Global-Health-Engineering/sitting-UDDT/drawings/user_interface_over_seat.pdf

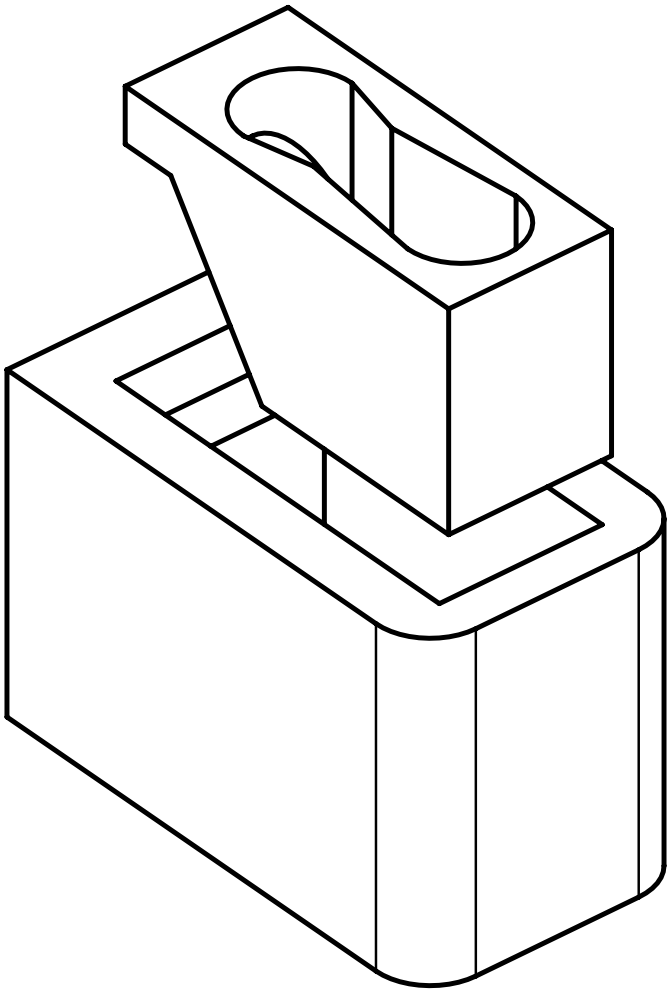
[picture p9: figure]
