Global-Health-Engineering/sitting-UDDT/drawings/EOOS_child_tech_4.pdf

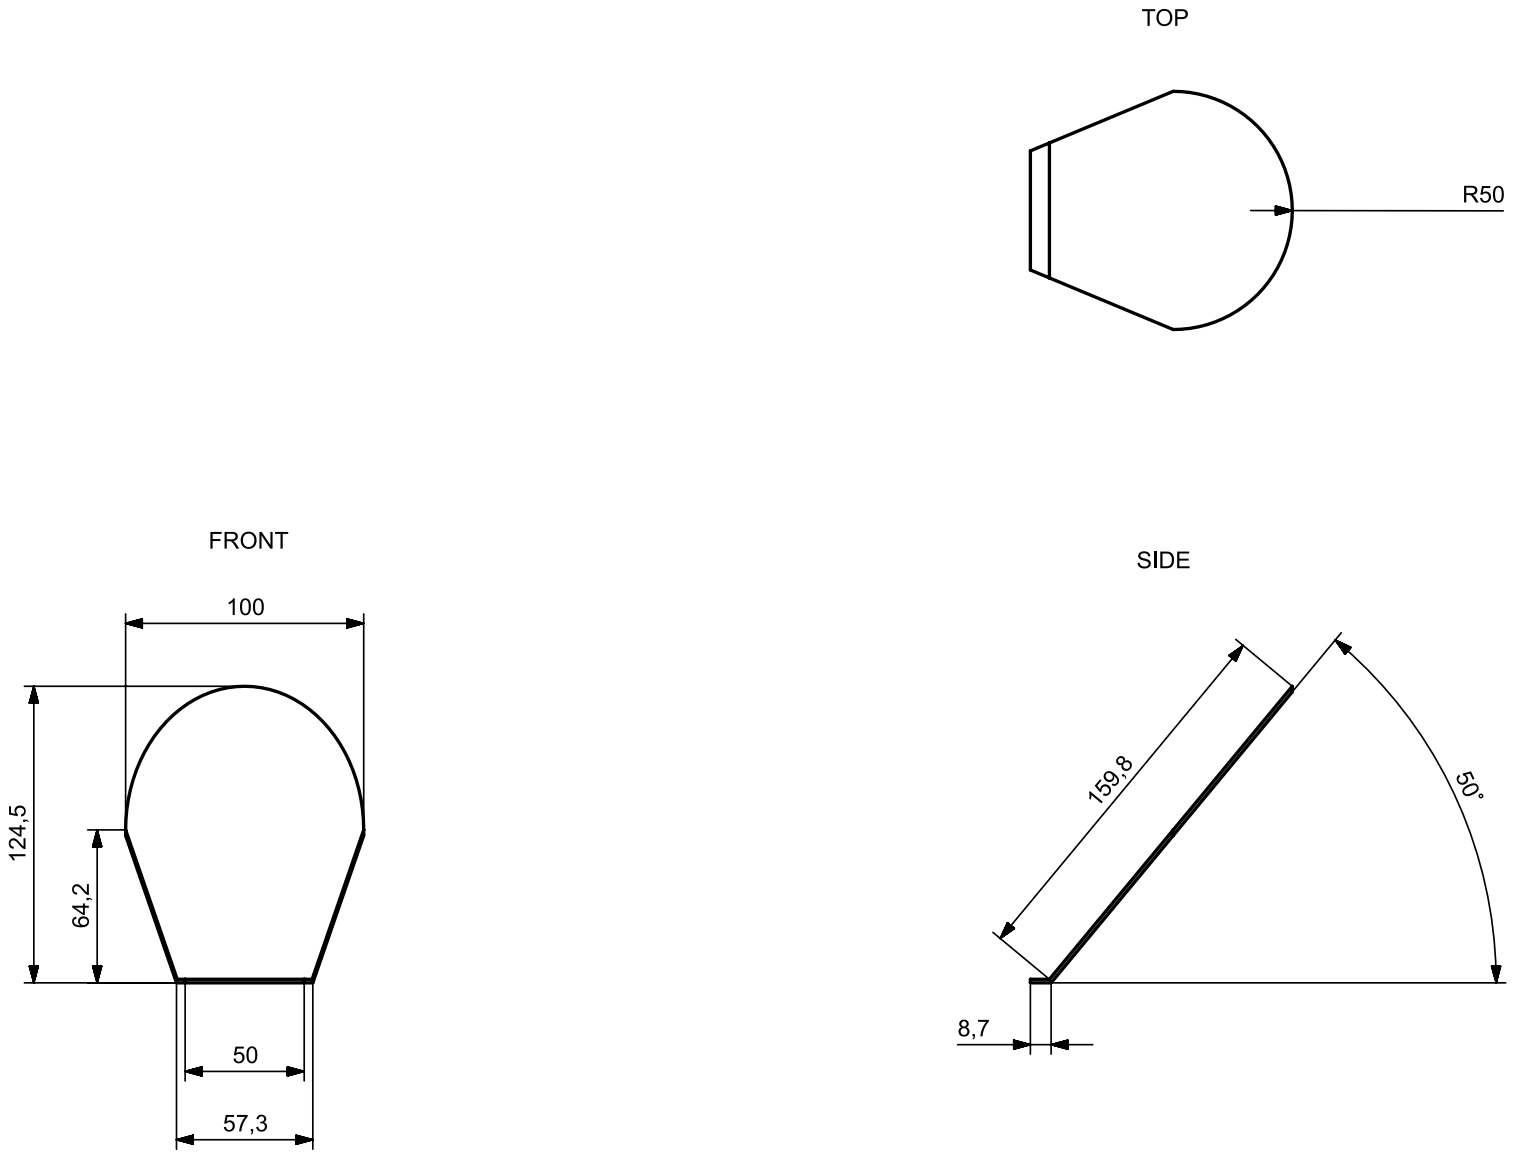
[picture p26: page 1]
