Global-Health-Engineering/sitting-UDDT/drawings/EOOS_child_tech_5.pdf

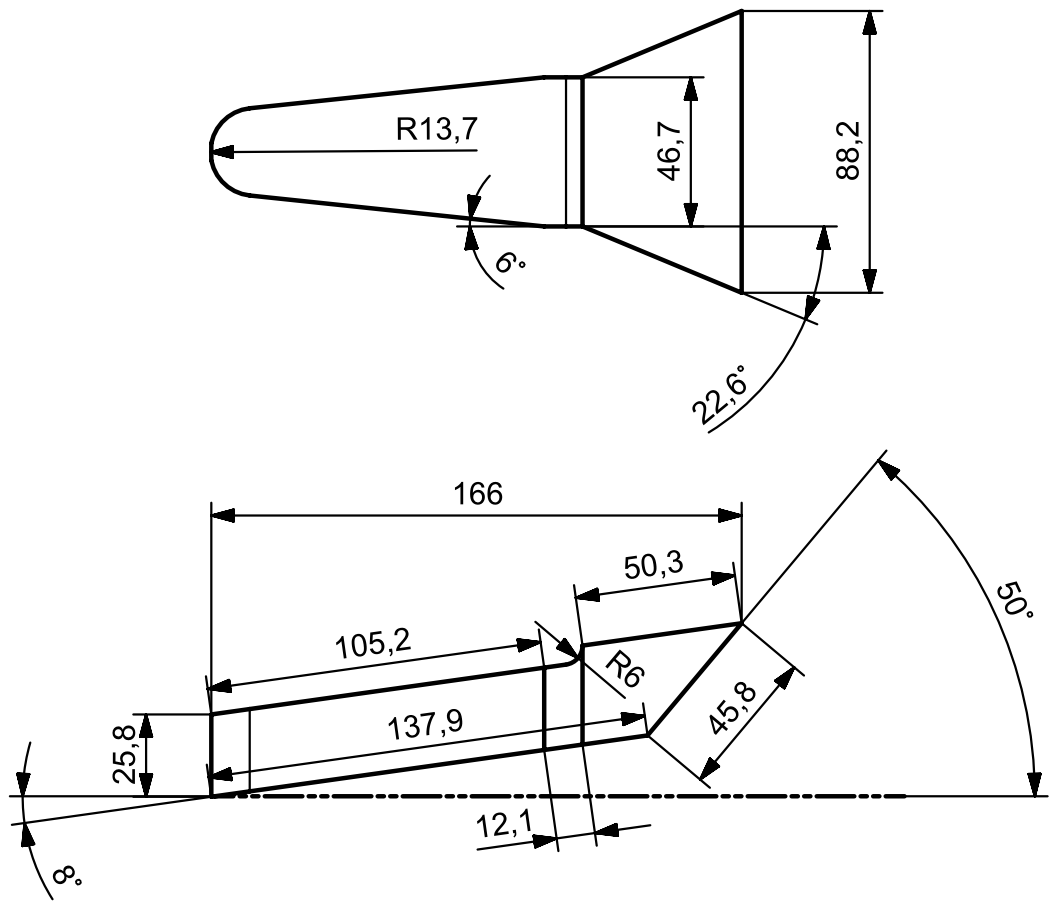
[picture p27: page 1]
