Global-Health-Engineering/sitting-UDDT/drawings/EOOS_child_tech_6.pdf

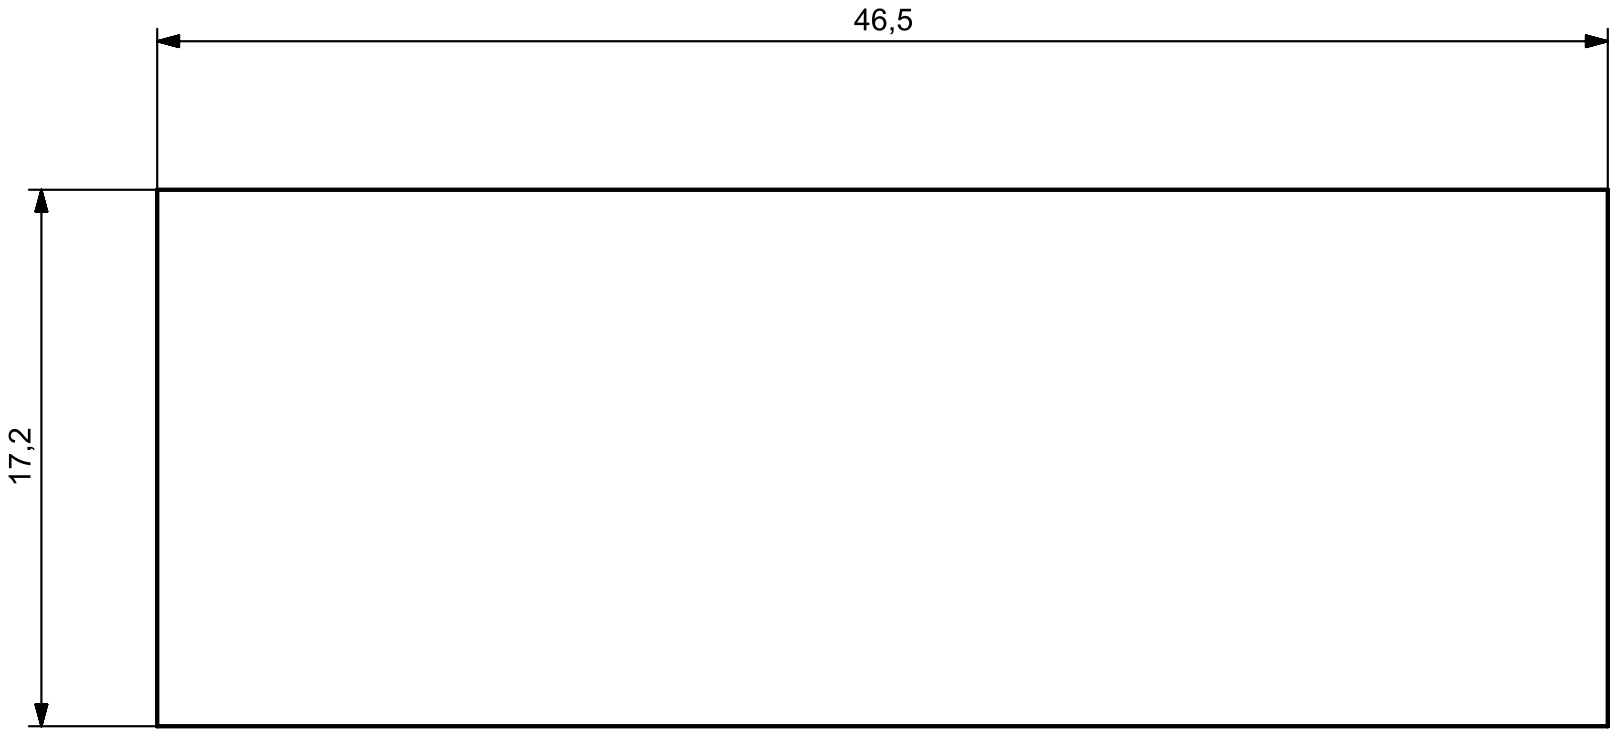
[picture p28: page 1]
