Global-Health-Engineering/sitting-UDDT/drawings/tech_seat_adult.pdf

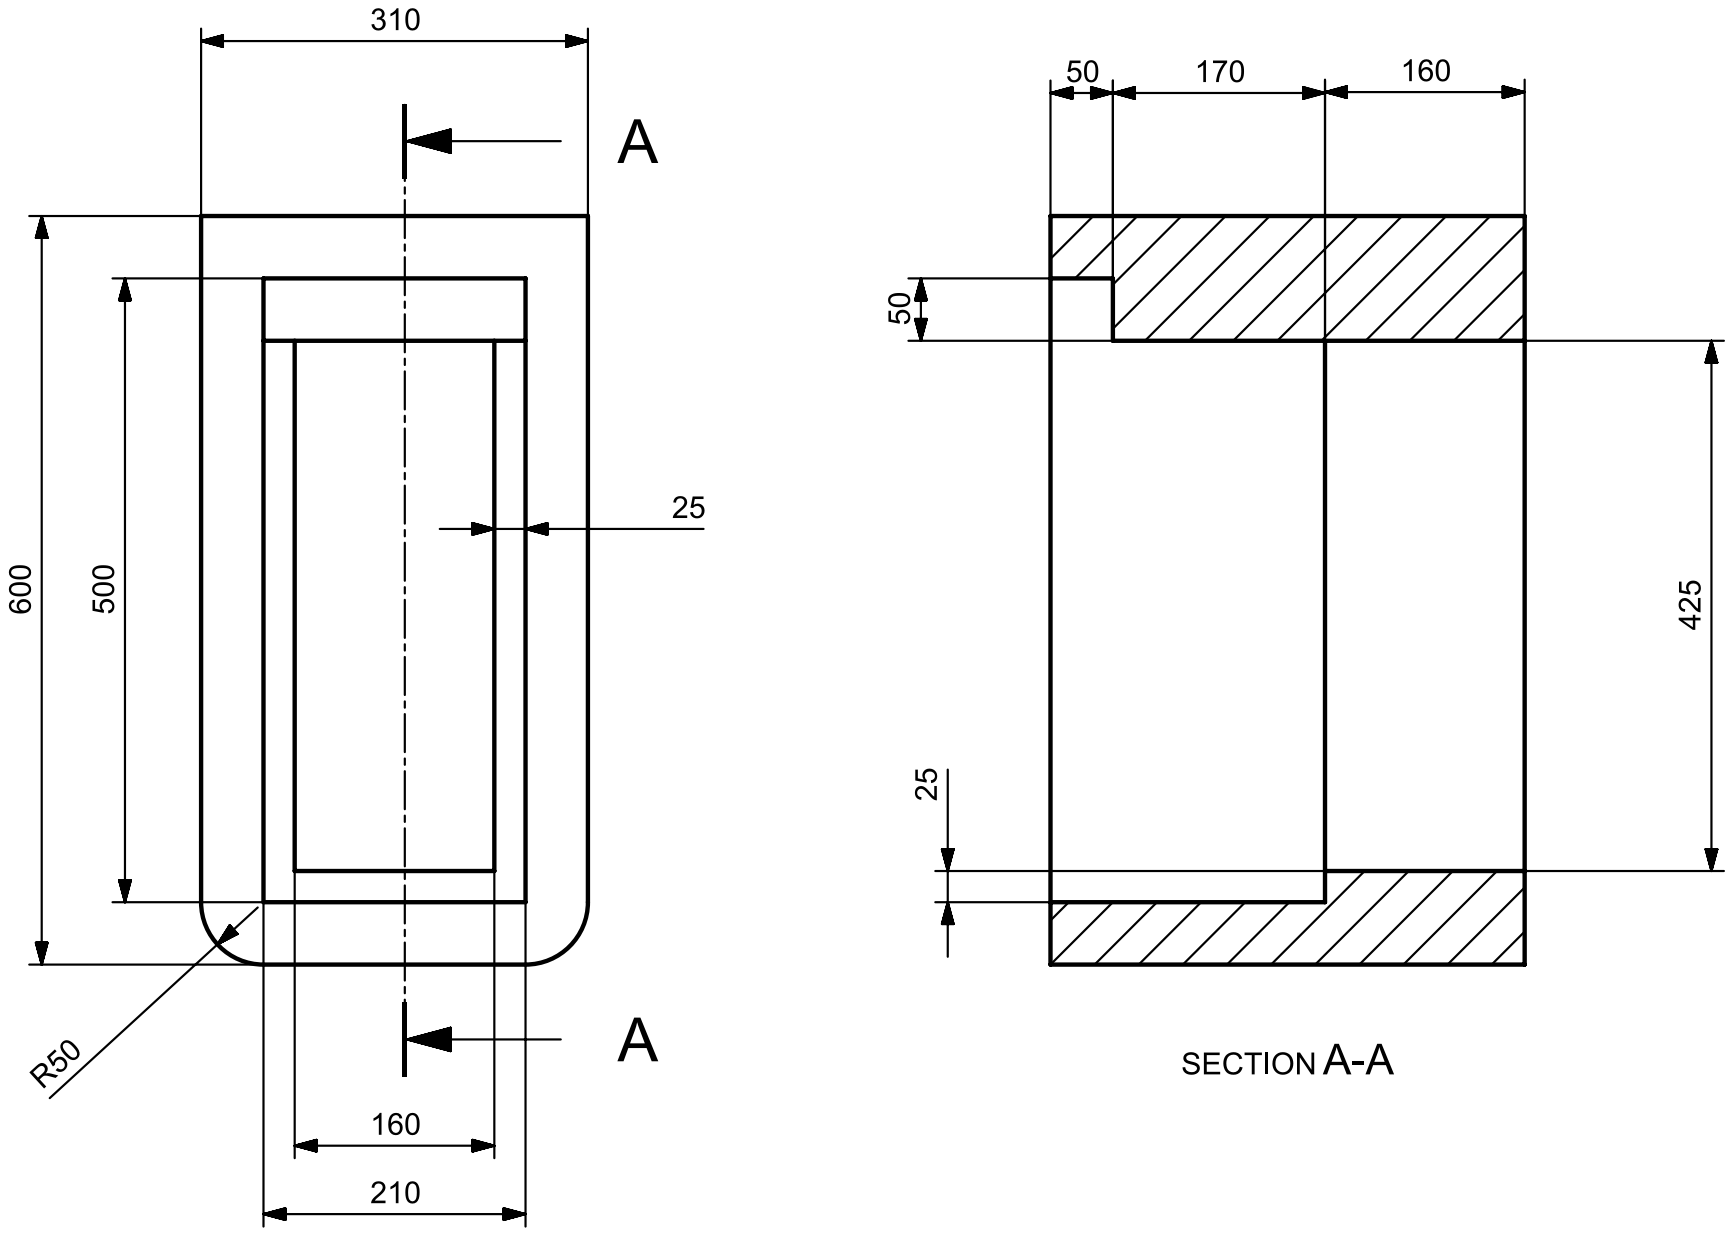
[picture p29: page 1]
