Global-Health-Engineering/sitting-UDDT/drawings/tech_seat_child.pdf

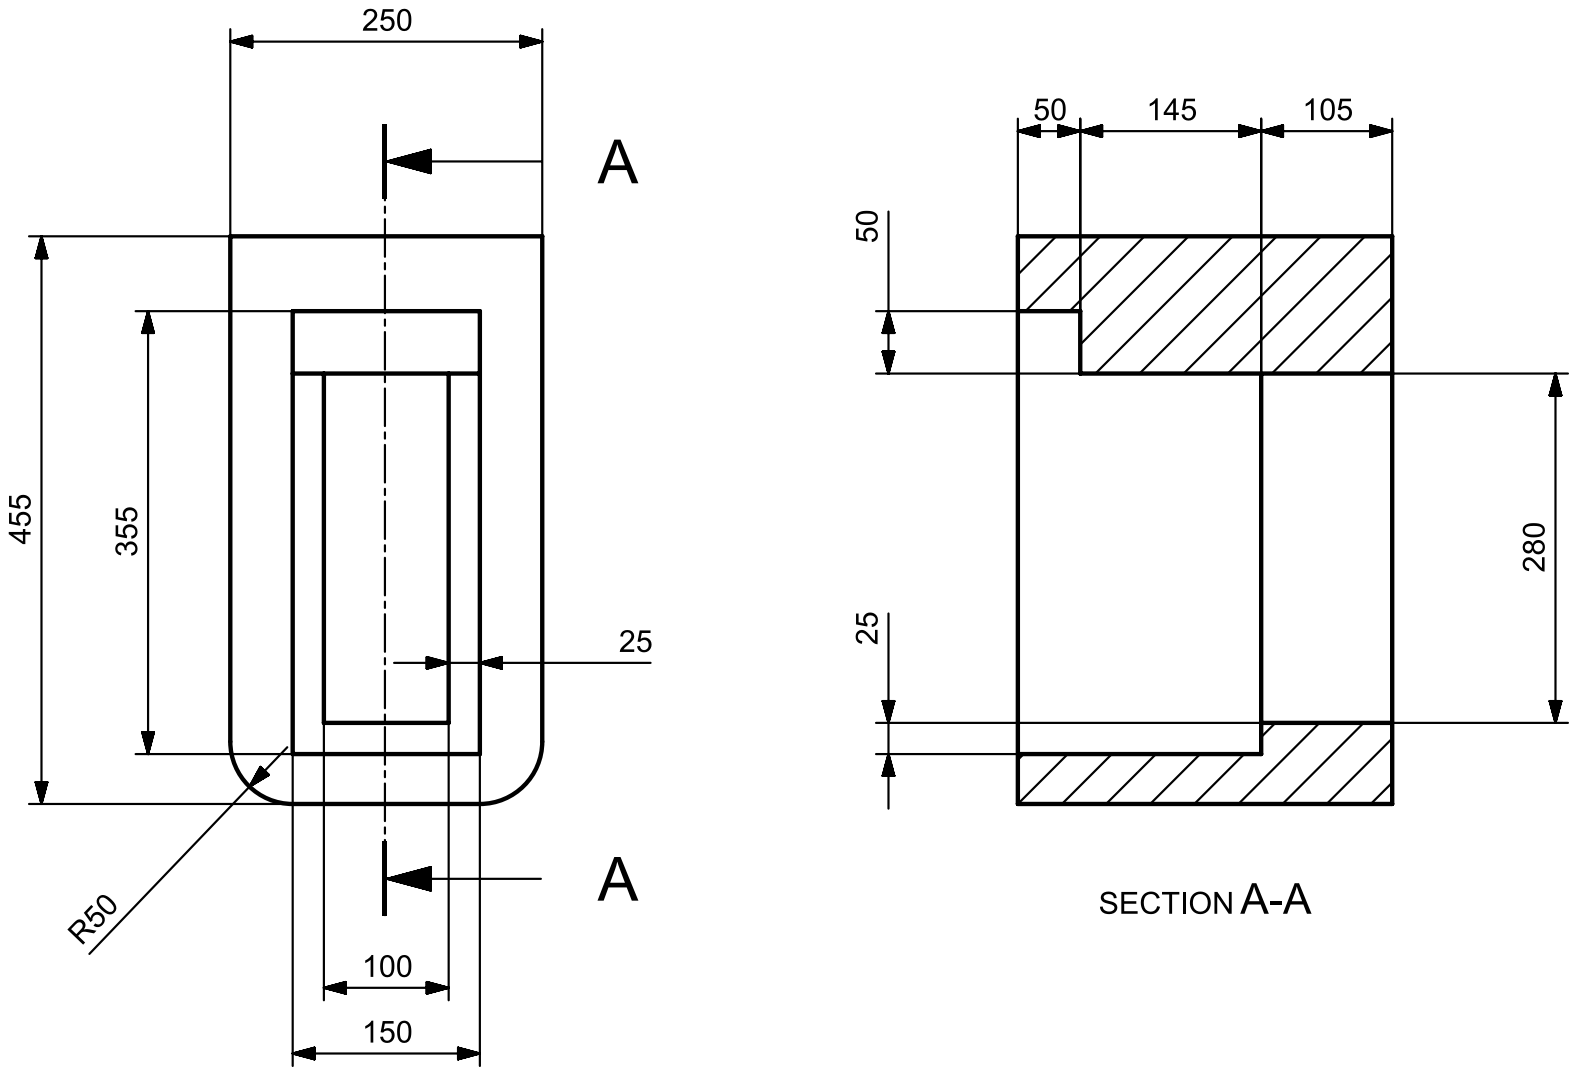
[picture p30: page 1]
